dumaiss/pBITzPlatform/99-KiCad-Lib/3D-Models/FT230XS-U.step

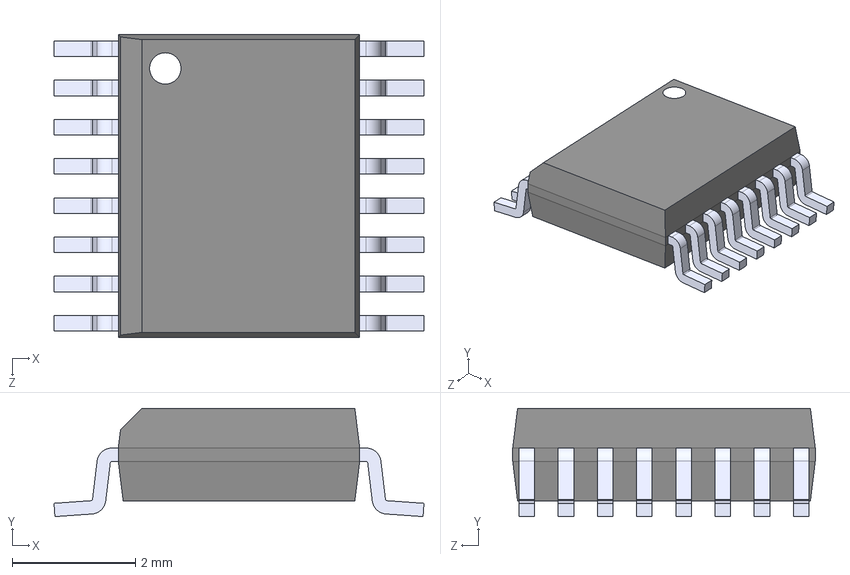
[picture p19: CAD file, 2026-06-17]
99-KiCad-Lib/3D-Models/FT230XS-U.step
5.99 x 1.75 x 4.90 mm
