dumaiss/pBITzPlatform/99-KiCad-Lib/3D-Models/EXB-2HV330JV.STEP

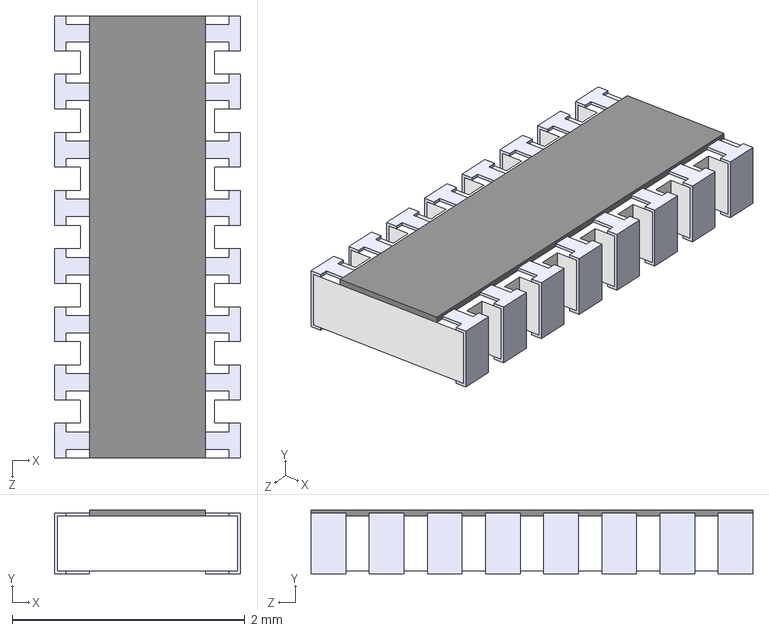
[picture p20: CAD file, 2026-06-17]
99-KiCad-Lib/3D-Models/EXB-2HV330JV.STEP
1.60 x 0.55 x 3.80 mm
