dumaiss/pBITzPlatform/99-KiCad-Lib/3D-Models/TSOP-44_MIL400_ALL.step

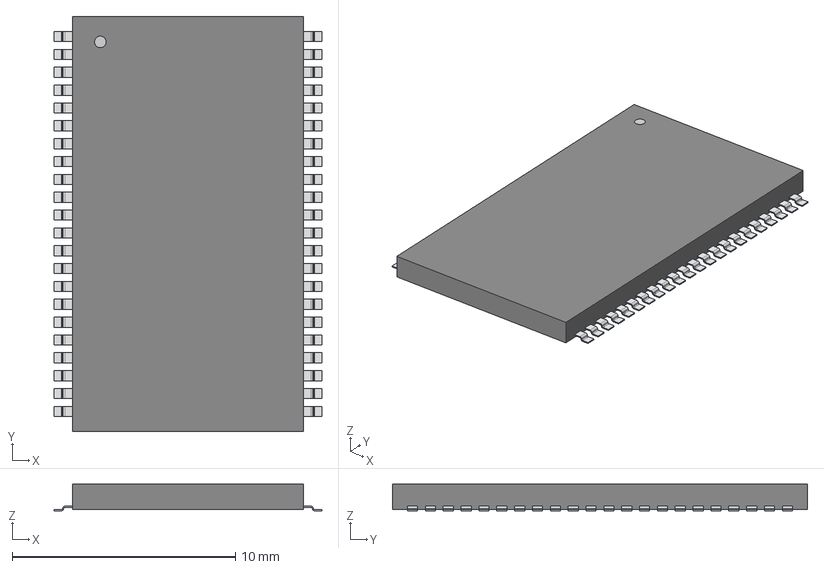
[picture p21: CAD file, 2026-06-17]
99-KiCad-Lib/3D-Models/TSOP-44_MIL400_ALL.step
12.0 x 18.6 x 1.20 mm
