dumaiss/pBITzPlatform/99-KiCad-Lib/3D-Models/4820p.stp

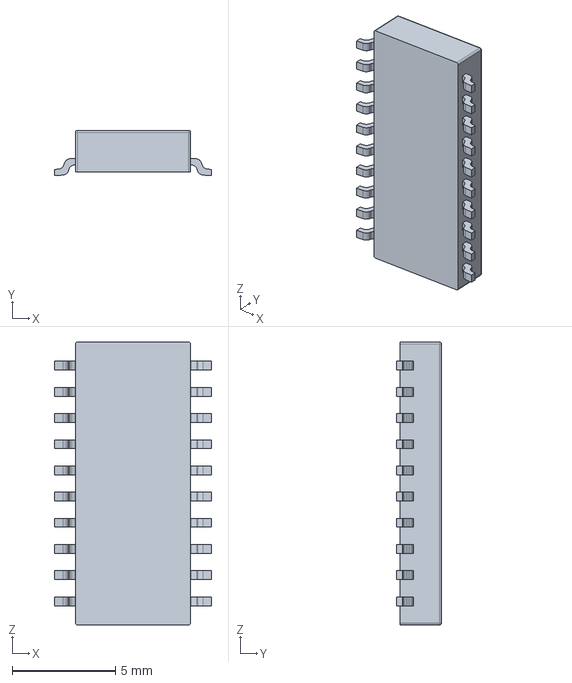
[picture p22: CAD file, 2026-06-17]
99-KiCad-Lib/3D-Models/4820p.stp
7.62 x 2.20 x 13.7 mm
