dumaiss/pBITzPlatform/99-KiCad-Lib/3D-Models/MAX3421EETJ_T.step

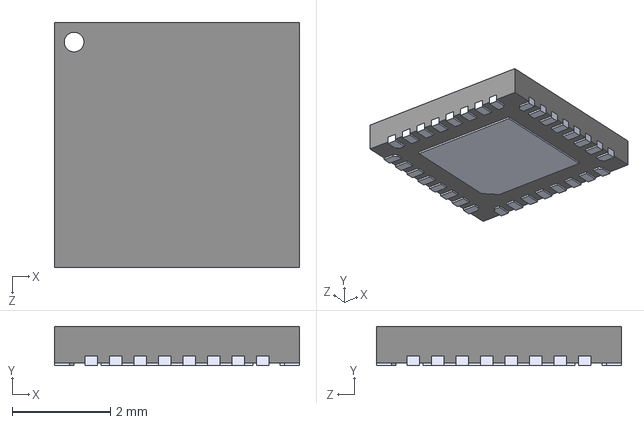
[picture p23: CAD file, 2026-06-17]
99-KiCad-Lib/3D-Models/MAX3421EETJ_T.step
5.00 x 0.8 x 5.00 mm
