dumaiss/pBITzPlatform/99-KiCad-Lib/3D-Models/LTC2954CTS8-2_TRMPBF.step

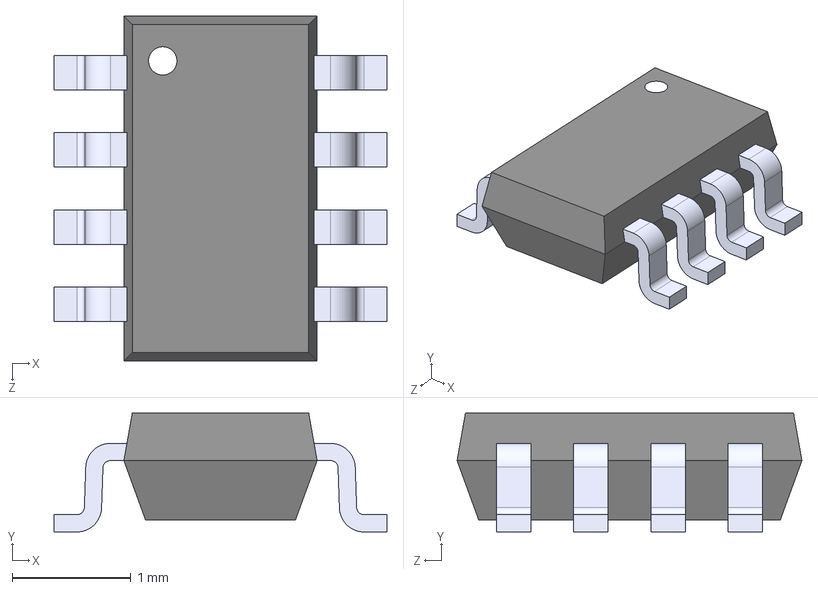
[picture p24: CAD file, 2026-06-17]
99-KiCad-Lib/3D-Models/LTC2954CTS8-2_TRMPBF.step
2.80 x 1.00 x 2.90 mm
