dumaiss/pBITzPlatform/99-KiCad-Lib/3D-Models/1-2199300-2.STEP

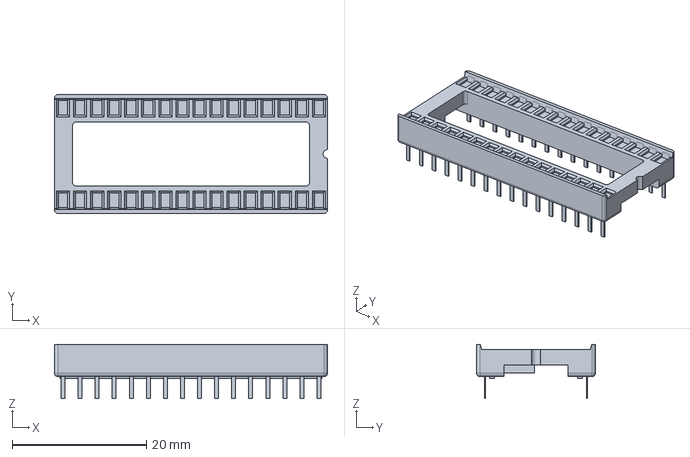
[picture p25: CAD file, 2026-06-17]
99-KiCad-Lib/3D-Models/1-2199300-2.STEP
40.6 x 17.7 x 8.10 mm
