dumaiss/pBITzPlatform/99-KiCad-Lib/3D-Models/C_ARRAY_EXB28V_PAN.step

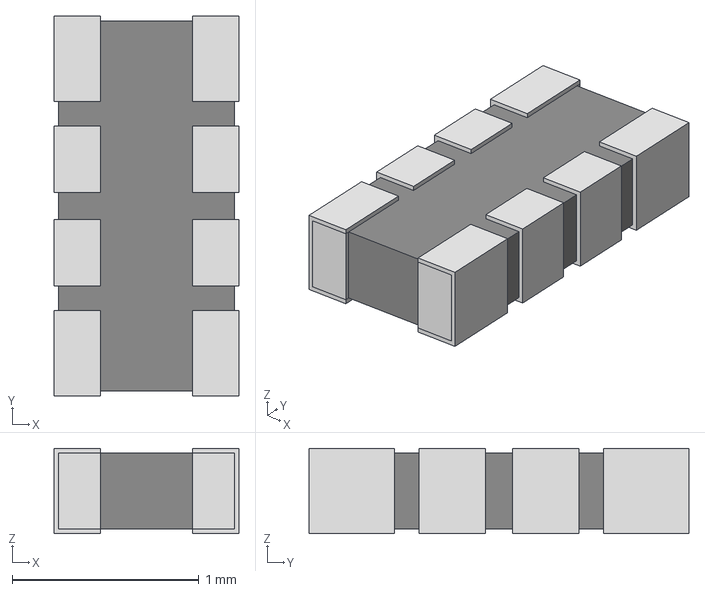
[picture p26: CAD file, 2026-06-17]
99-KiCad-Lib/3D-Models/C_ARRAY_EXB28V_PAN.step
0.99 x 2.03 x 0.457 mm
