dumaiss/pBITzPlatform/99-KiCad-Lib/3D-Models/D0016A.stp

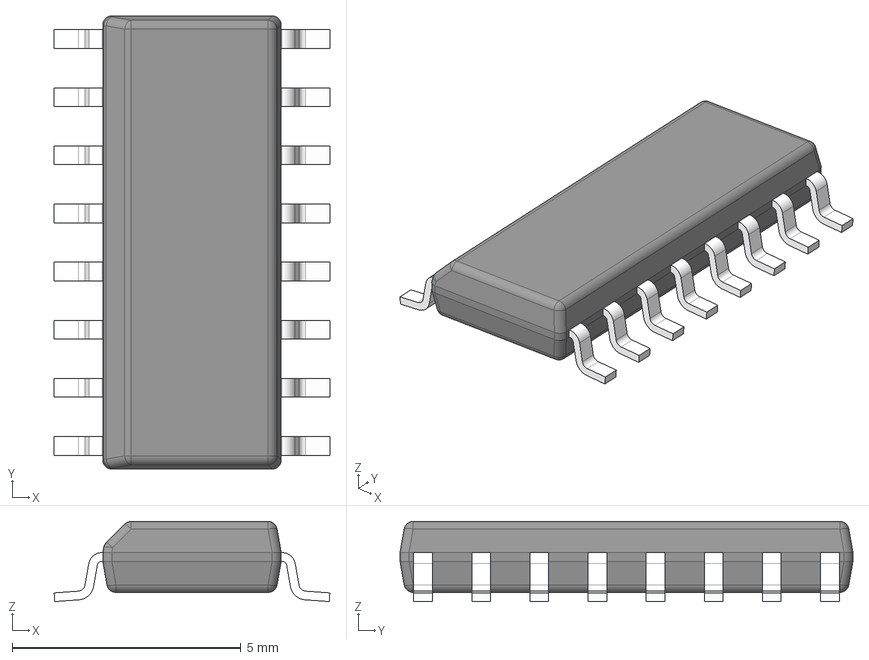
[picture p27: CAD file, 2026-06-17]
99-KiCad-Lib/3D-Models/D0016A.stp
6.03 x 9.90 x 1.75 mm
BODY-SO
LEAD-SO x 16
PIN1-ID
