dumaiss/pBITzPlatform/99-KiCad-Lib/3D-Models/RCJ-32265.step

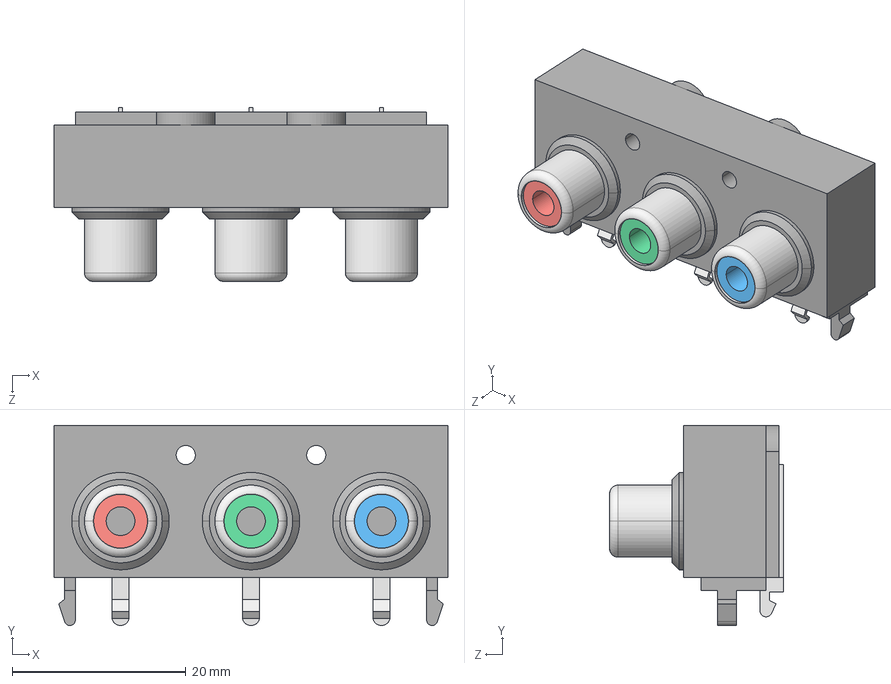
[picture p28: CAD file, 2026-06-17]
99-KiCad-Lib/3D-Models/RCJ-32265.step
45.3 x 23.0 x 20.0 mm
RCJ-32_RCJ-32
PLUG_Red
PLUG_Green
PLUG_Blue
