dumaiss/pBITzPlatform/99-KiCad-Lib/3D-Models/socket_a_40-lc-tt.stp

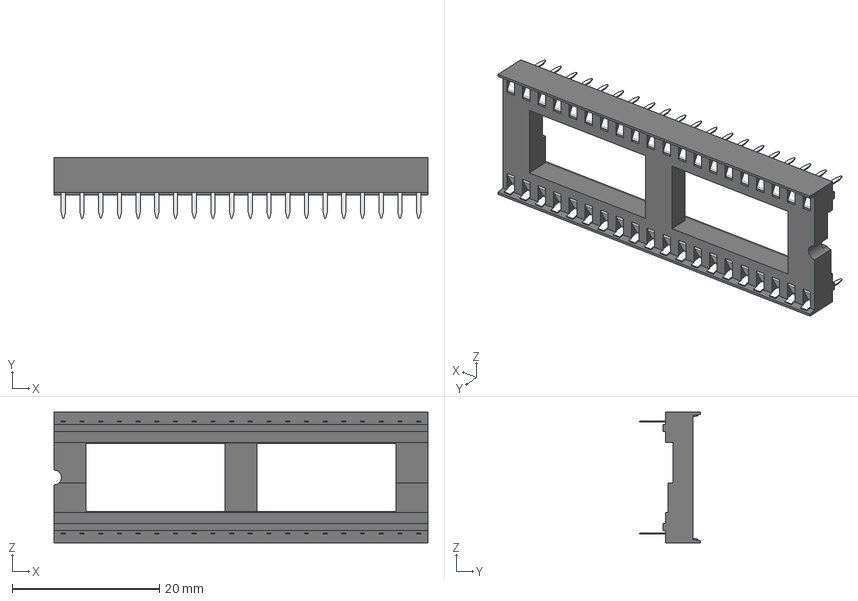
[picture p29: CAD file, 2026-06-17]
99-KiCad-Lib/3D-Models/socket_a_40-lc-tt.stp
50.8 x 8.25 x 17.8 mm
