dumaiss/pBITzPlatform/99-KiCad-Lib/3D-Models/PJ-037A.step

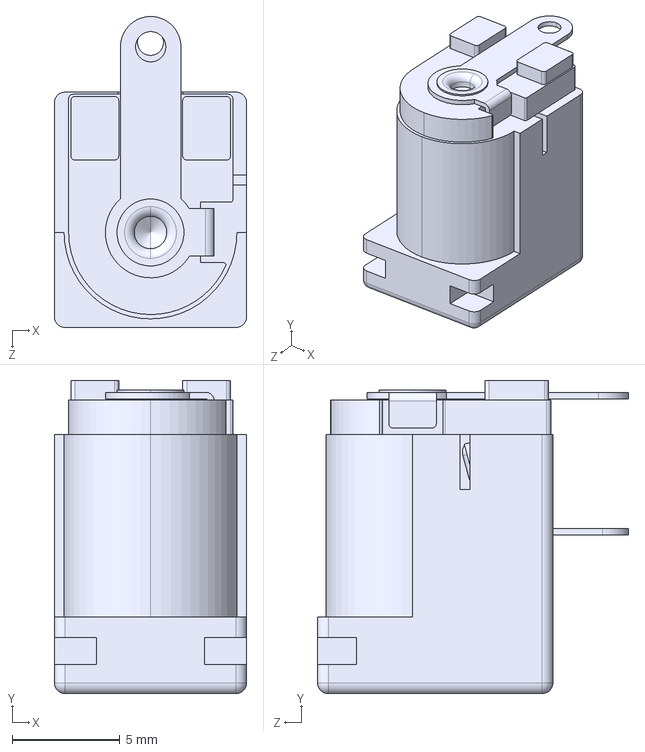
[picture p30: CAD file, 2026-06-17]
99-KiCad-Lib/3D-Models/PJ-037A.step
8.90 x 14.5 x 14.4 mm
