dumaiss/pBITzPlatform/99-KiCad-Lib/3D-Models/EXB-E10C472J.step

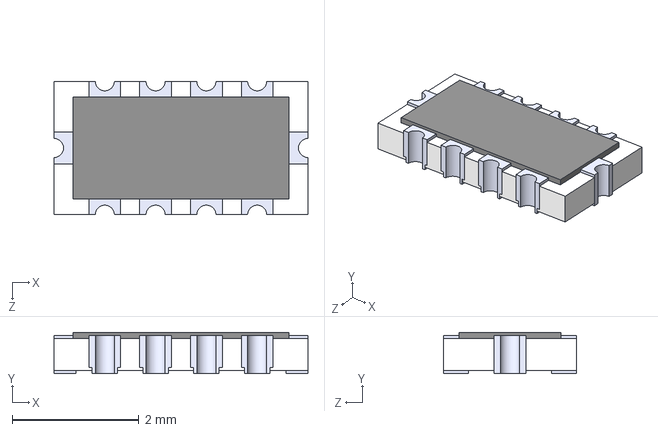
[picture p31: CAD file, 2026-06-17]
99-KiCad-Lib/3D-Models/EXB-E10C472J.step
4.00 x 0.65 x 2.10 mm
