dumaiss/pBITzPlatform/99-KiCad-Lib/3D-Models/ECS-2100AX-147.4.step

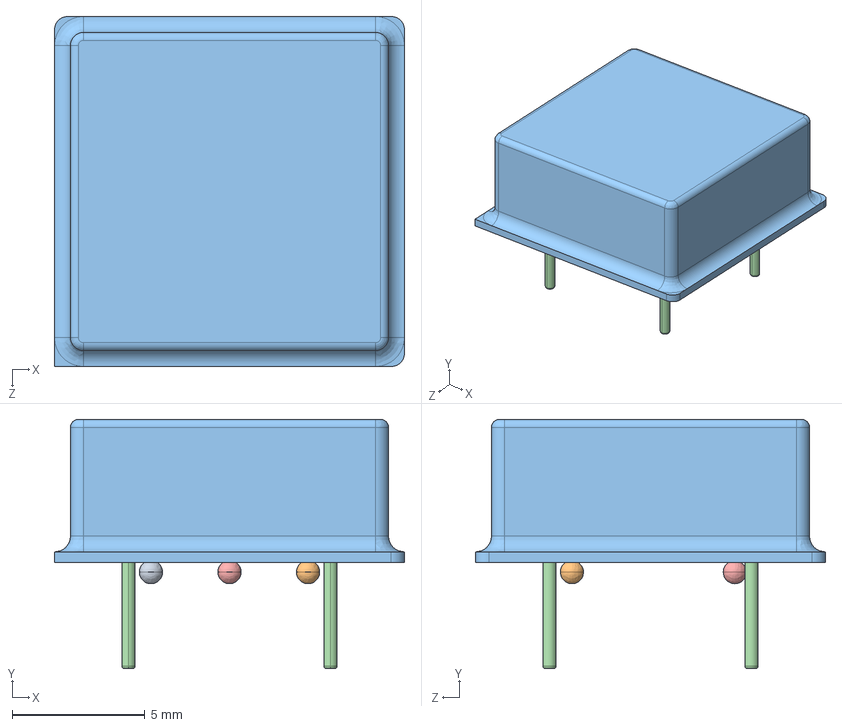
[picture p32: CAD file, 2026-06-17]
99-KiCad-Lib/3D-Models/ECS-2100AX-147.4.step
13.2 x 9.40 x 13.2 mm
